spacelab-ufsc/interface-board/hardware/outputs/board_schematics/board_full_pdf_iip_charge.PDF

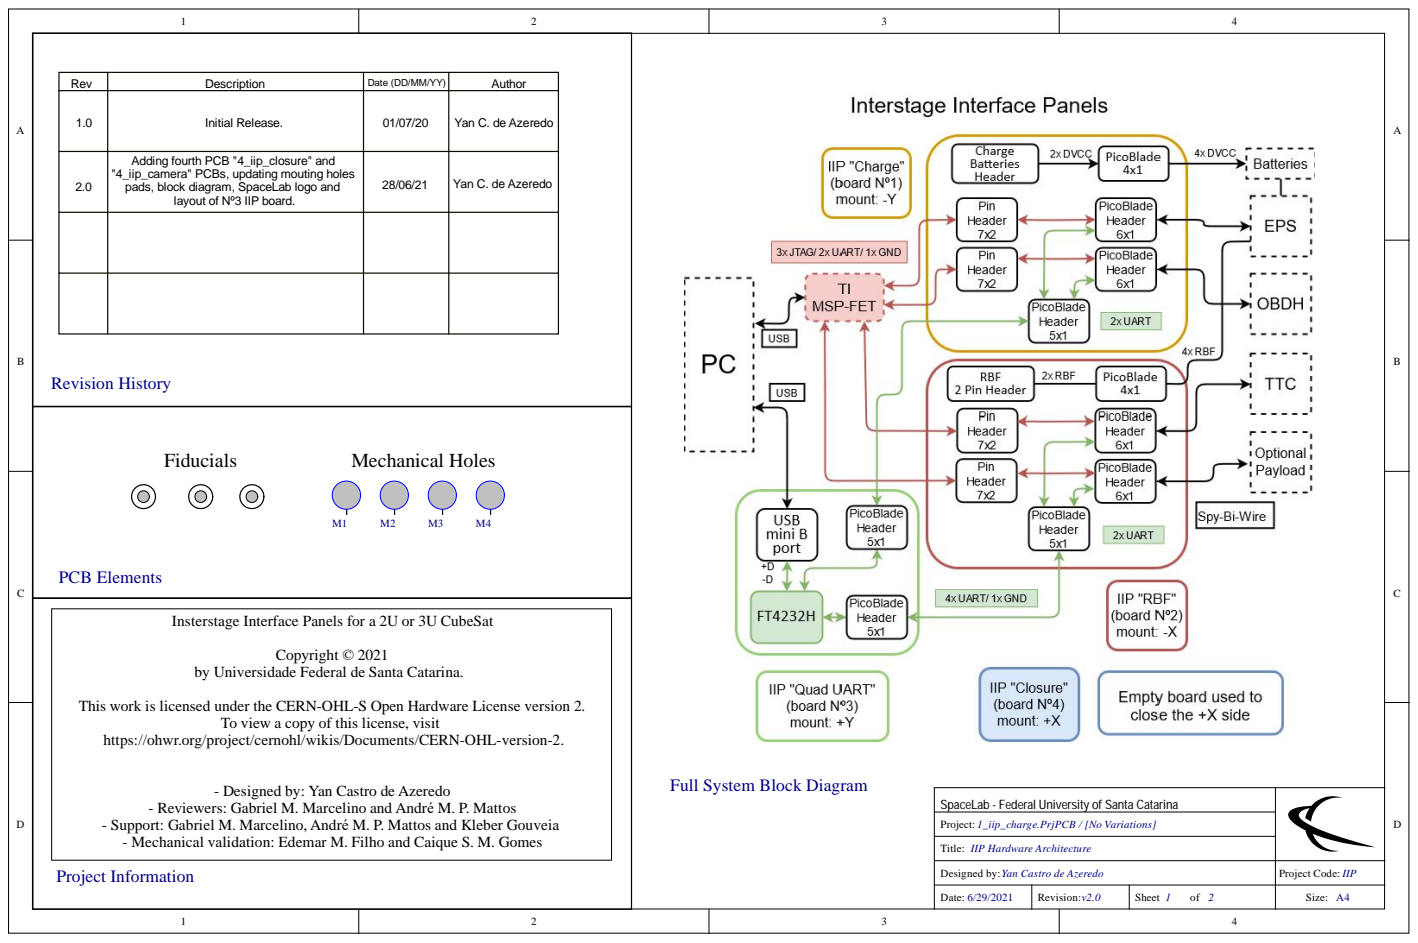
[picture p55: page 1]

R e v | D escri p t i o n | D a t e (D D /MM/YY) | Au t h o r

1 . 0 | I n i t i a l R e l e ase . | 0 1 / 0 7/2 0 | Ya n C . d e Azere d o

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

Insterstage Interface Panels for a 2U or 3U CubeSat

Universidade Federal de Santa Catarina.

the CERN-O
To view a copy of
.org/project/cernohl

Full System Block Diagram

ceLab - Federal University of S

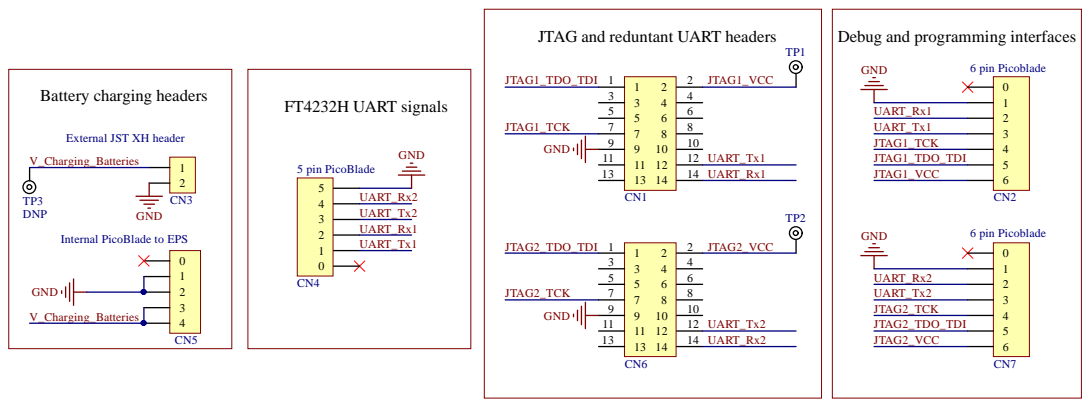
[picture p56: page 2]

tery charging headers External JST XH header

ceLab - Federal University of S

Des i g ned b y : Ya n Ca s t ro de A zered o | Project Co de: IIPN1

Date: 6 / 2 9 / 2 0 2 1 | Rev i s i o n : v2.0 | Sheet 2 o f 2 | Size: A 4

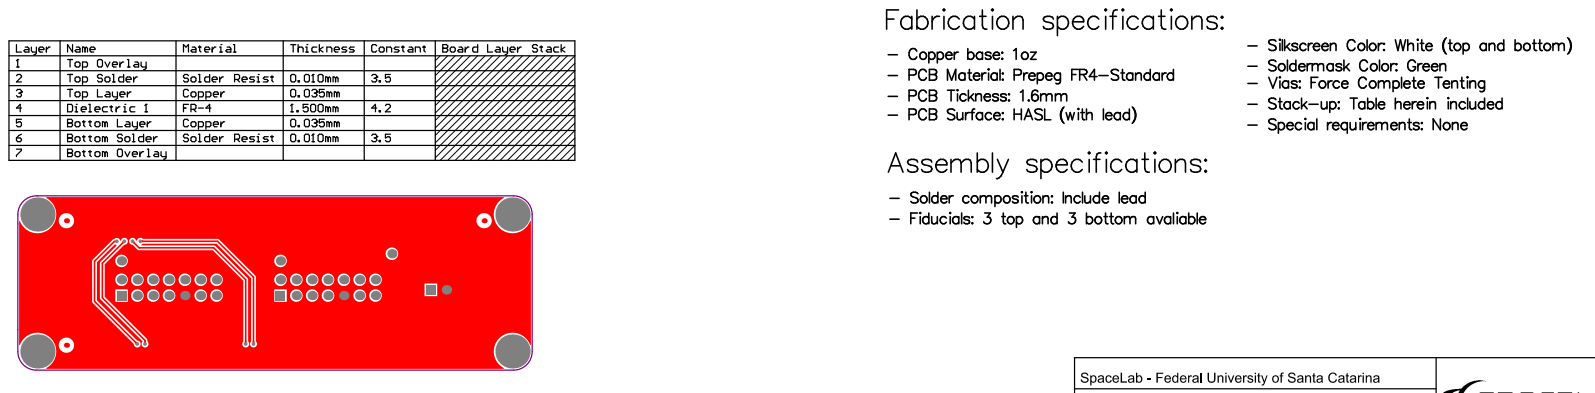
[picture p57: page 3]

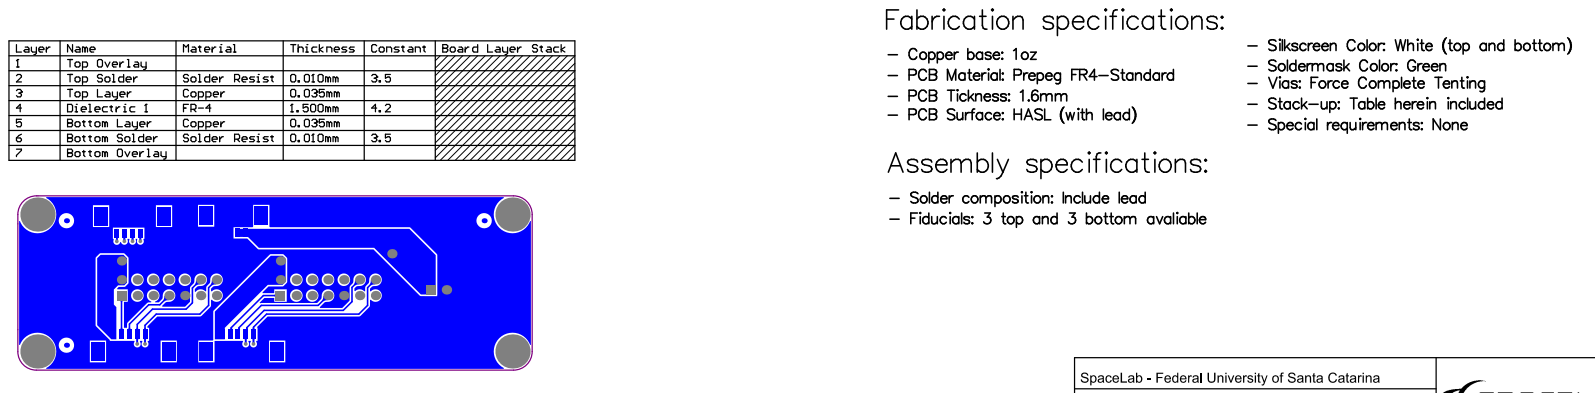
[picture p58: page 4]

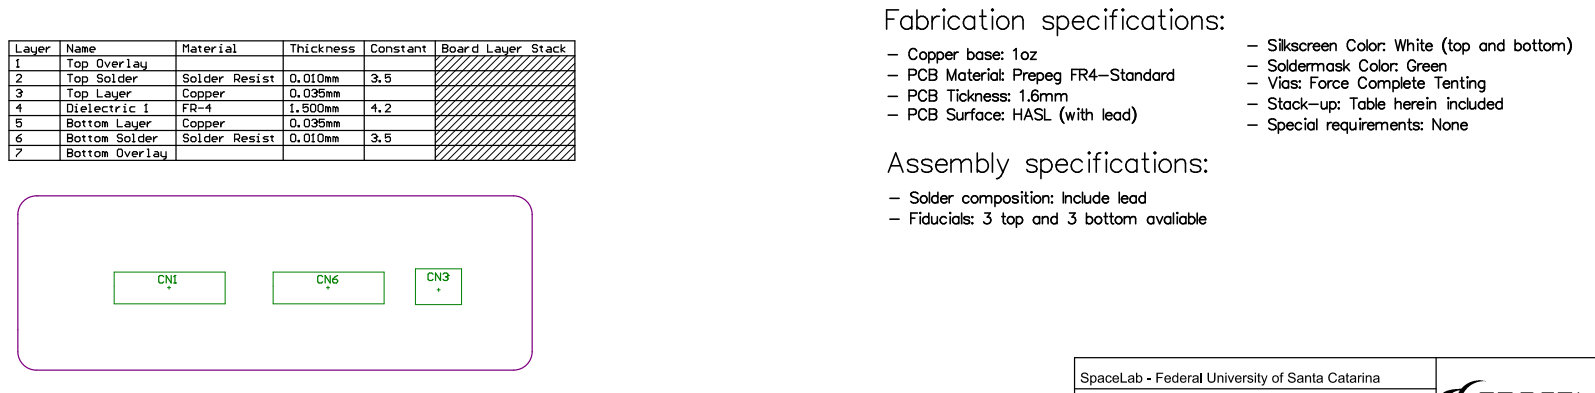
[picture p59: page 5]

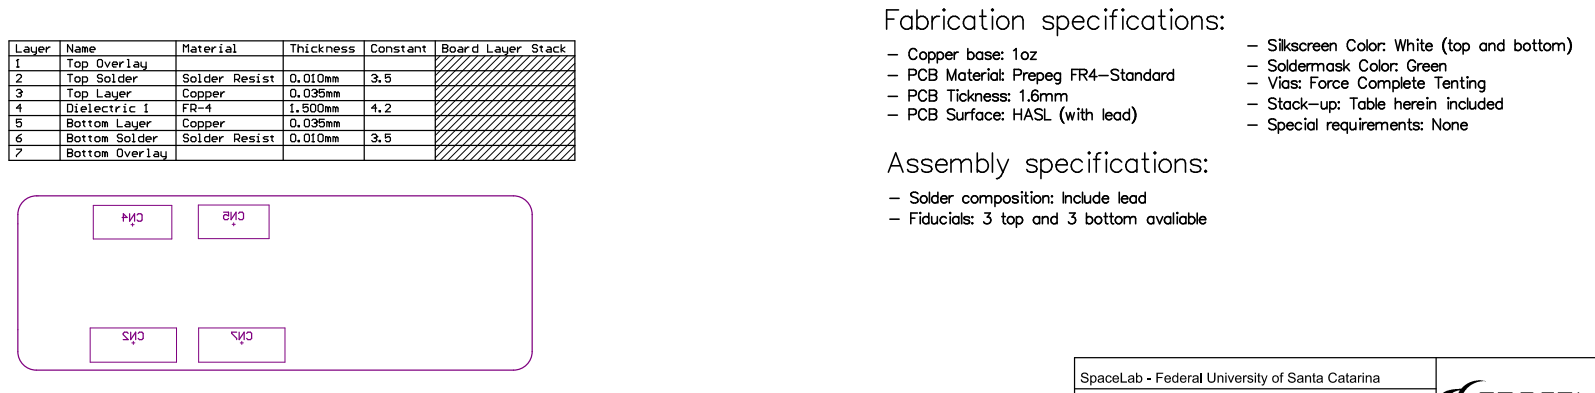
[picture p60: page 6]

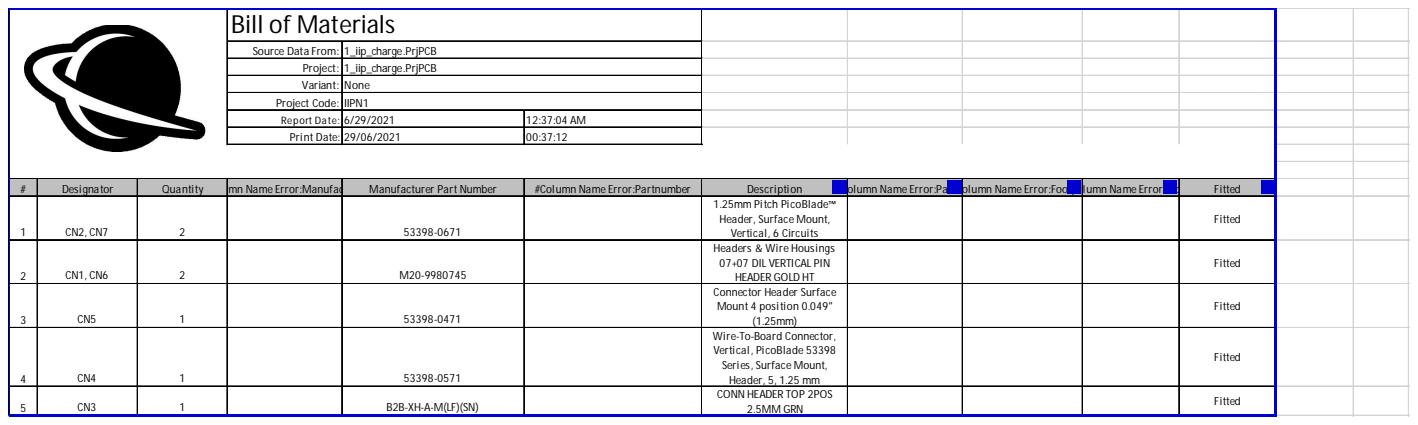
[picture p61: page 7]

Bill of Materials

Source Data From: | 1_iip_charge.PrjPCB

Project: | 1_iip_charge.PrjPCB
Variant: | None
Project Code: | IIPN1
Report Date: | 6/29/2021 | 12:37:04 AM
Print Date: | 29/06/2021 | 00:37:12

# | Designator | Quantity#Column Name Error:Manufac | Manufacturer Part Number | #Column Name Error:Partnumber | Description #Column Name Error:Pac#kaColumn Name Error:Foo#tCoprlumn Name Error:Mo | Fitted
1 | CN2, CN7 | 2 | 53398-0671 | | 1.25mm Pitch PicoBlade™ Header, Surface Mount, Vertical, 6 Circuits | Fitted

2 | CN1, CN6 | 2 | M20-9980745 | | Headers & Wire Housings 07+07 DIL VERTICAL PIN HEADER GOLD HT | Fitted

3 | CN5 | 1 | 53398-0471 | | Connector Header Surface Mount 4 position 0.049" (1.25mm) | Fitted

4 | CN4 | 1 | 53398-0571 | | Wire-To-Board Connector, Vertical, PicoBlade 53398 Series, Surface Mount, Header, 5, 1.25 mm | Fitted

5 | CN3 | 1 | B2B-XH-A-M(LF)(SN) | | CONN HEADER TOP 2POS 2.5MM GRN | Fitted
