spacelab-ufsc/interface-board/hardware/outputs/board_schematics/board_full_pdf_iip_quad_uart.PDF

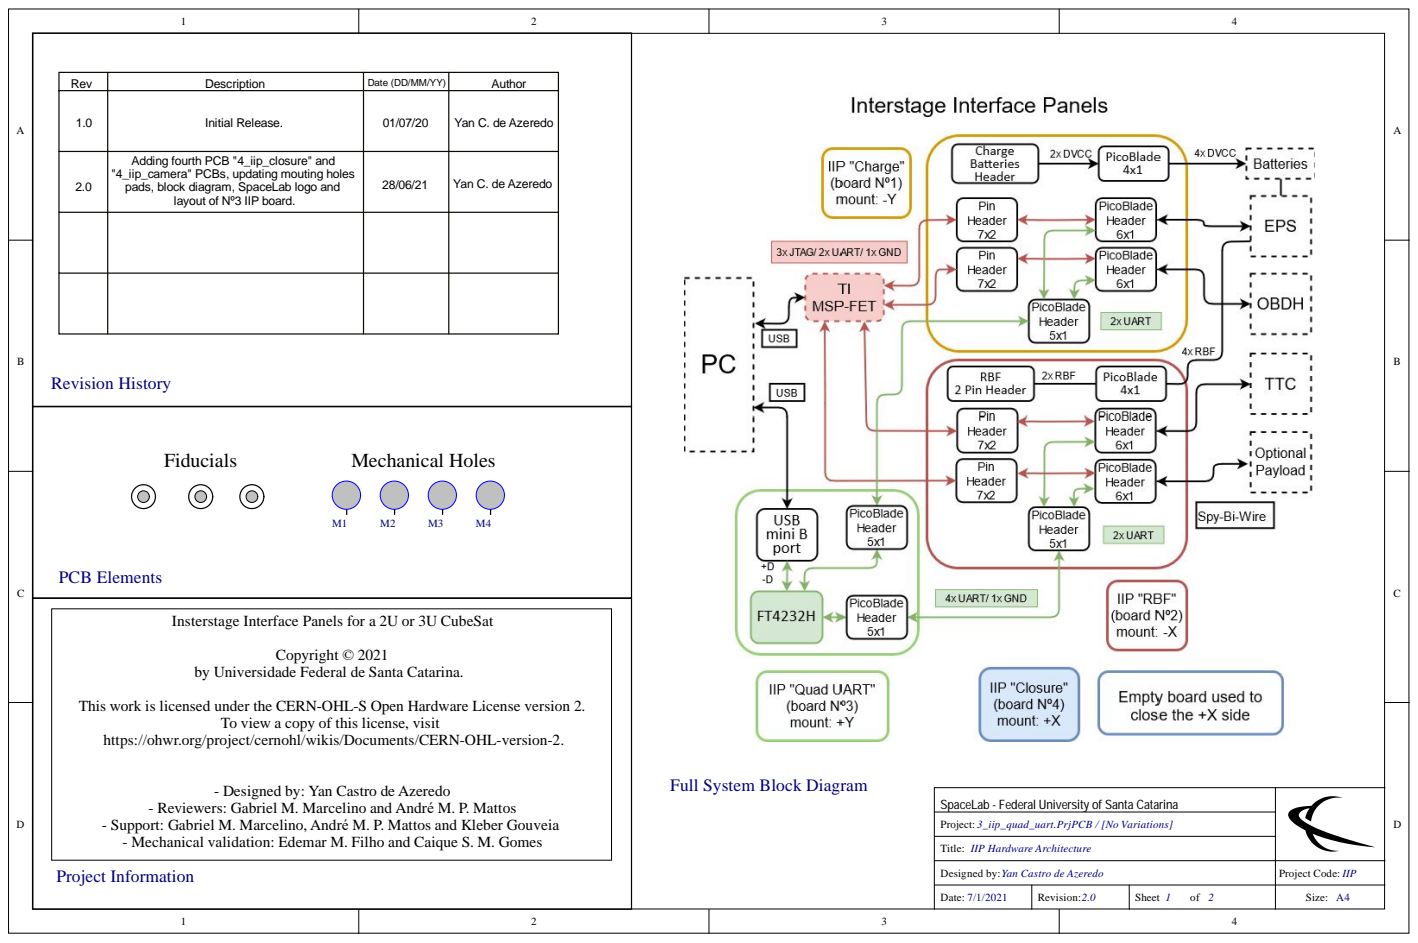
[picture p62: page 1]

R e v | D escri p t i o n | D a t e (D D /MM/YY) | Au t h o r

1 . 0 | I n i t i a l R e l e ase . | 0 1 / 0 7/2 0 | Ya n C . d e Azere d o

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

Insterstage Interface Panels for a 2U or 3U CubeSat

Universidade Federal de Santa Catarina.

the CERN-O
To view a copy of
.org/project/cernohl

Full System Block Diagram

SpaceLab - Federal University of S

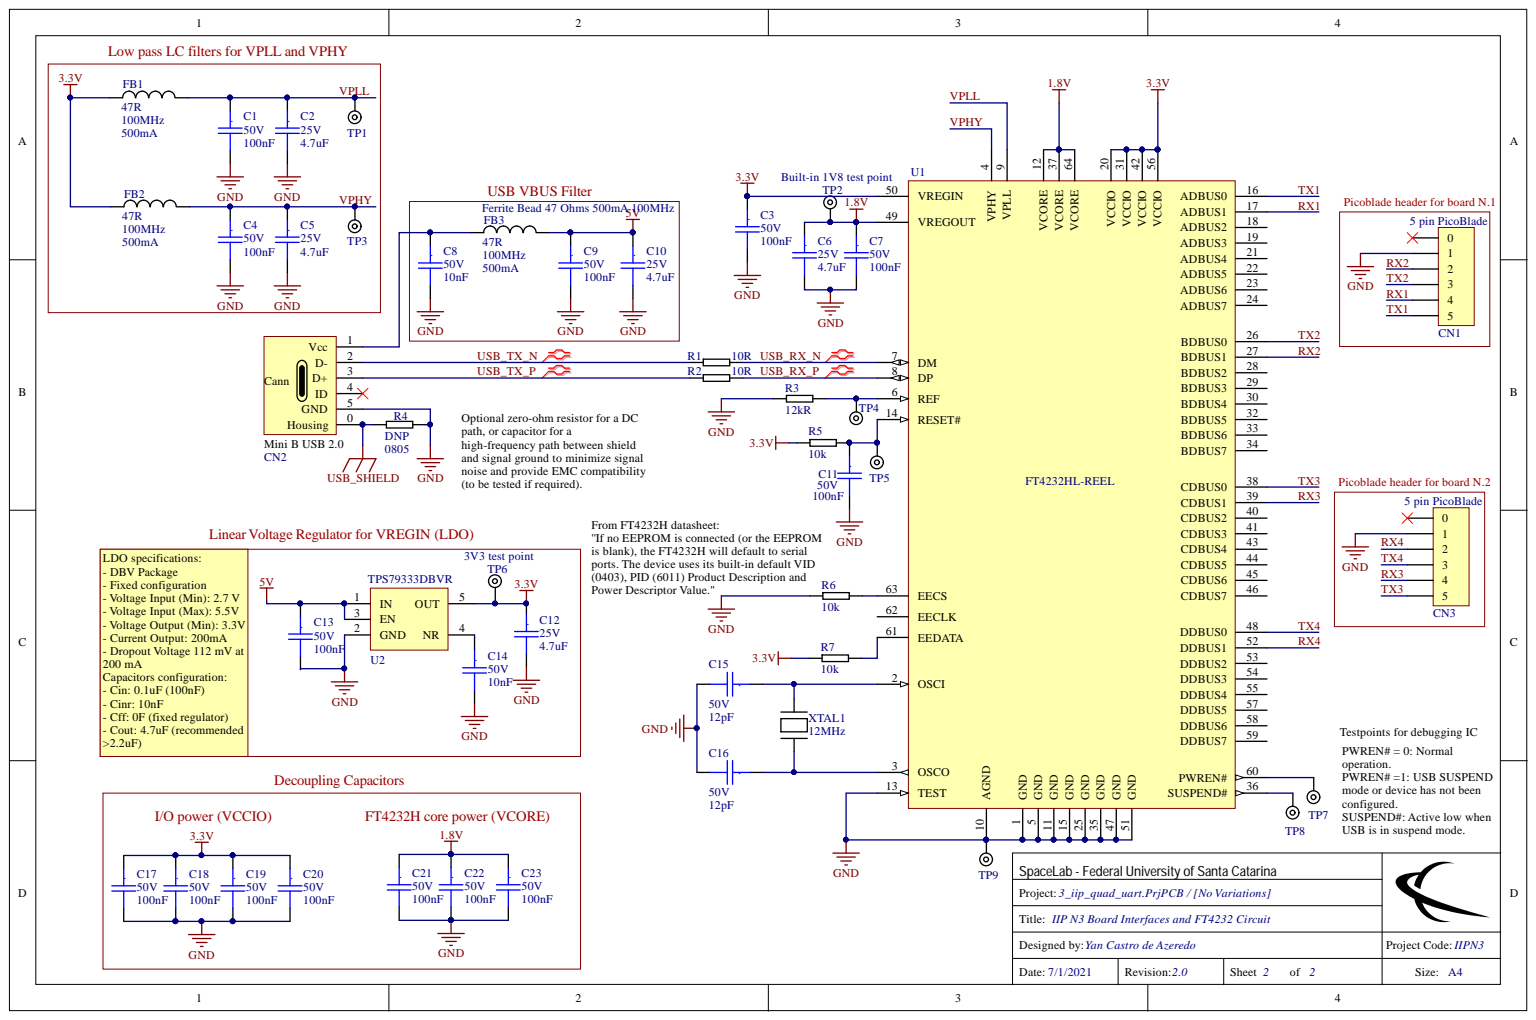
[picture p63: page 2]

ass LC filters for VPLL a

ulator for VREGIN (LDO)

SpaceLab - Federal University of S

t2 Des i g ned b y : Ya n Ca s t ro de A zered o | Project Co de: IIPN3

Date: 7 / 1 / 2 0 2 1 | Rev i s i o n : 2.0 | Sheet o f 2 | Size: A 4

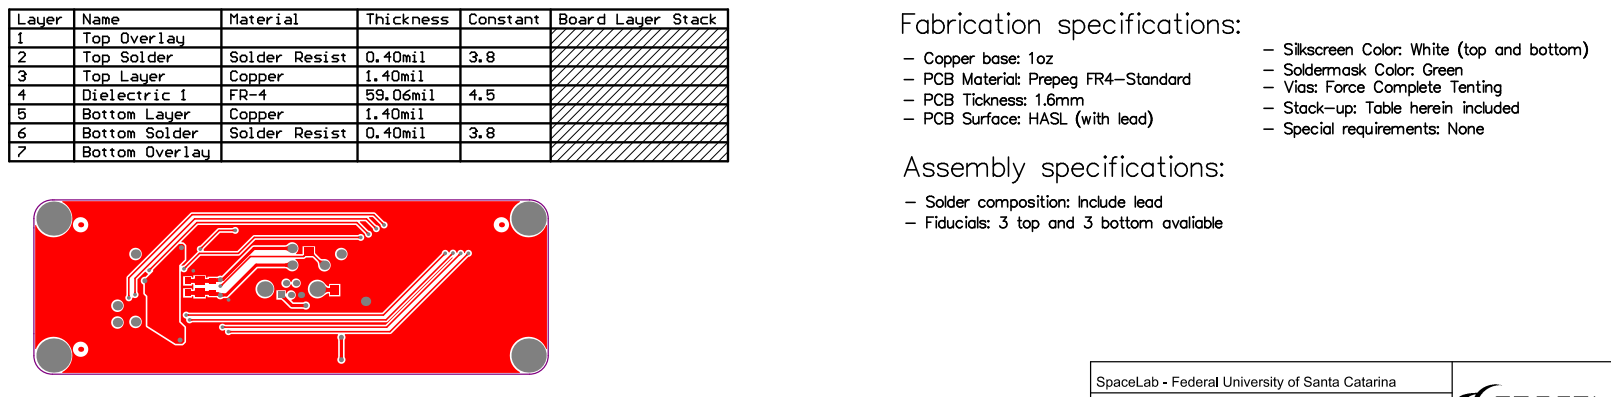
[picture p64: page 3]

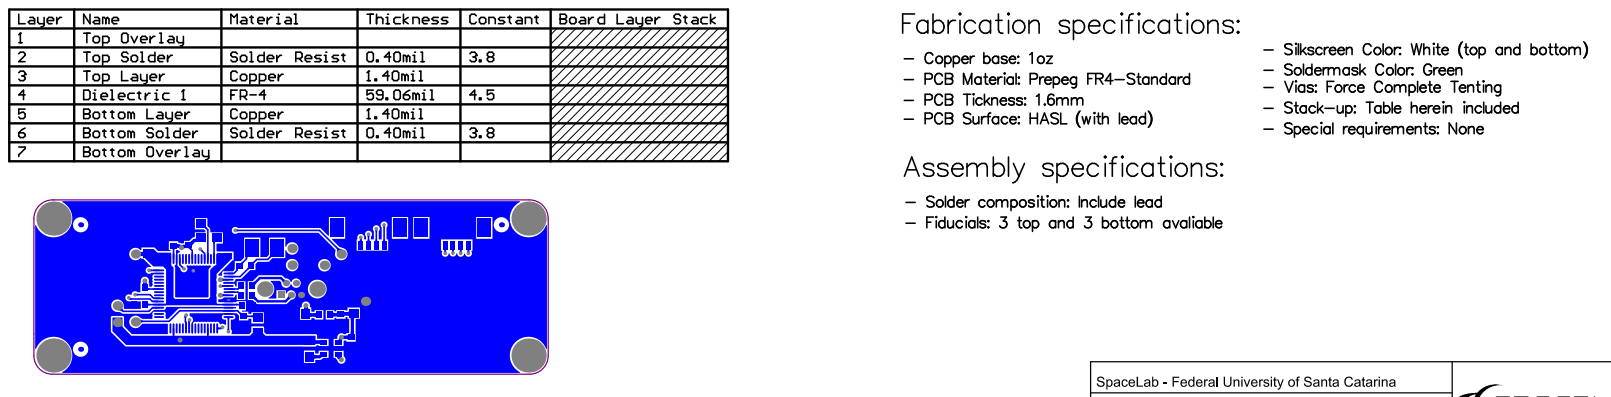
[picture p65: page 4]

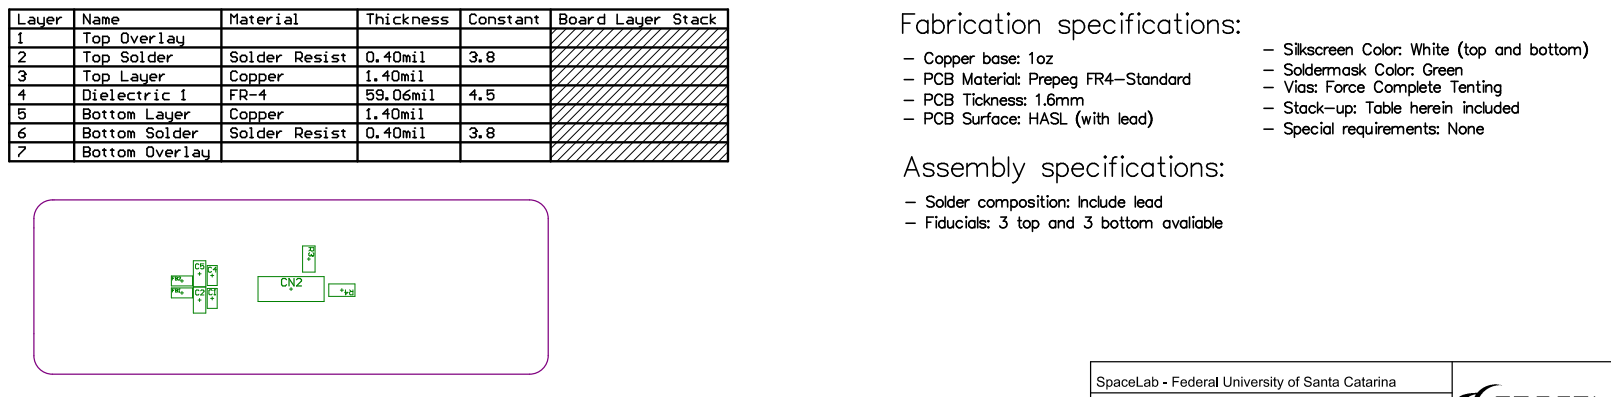
[picture p66: page 5]

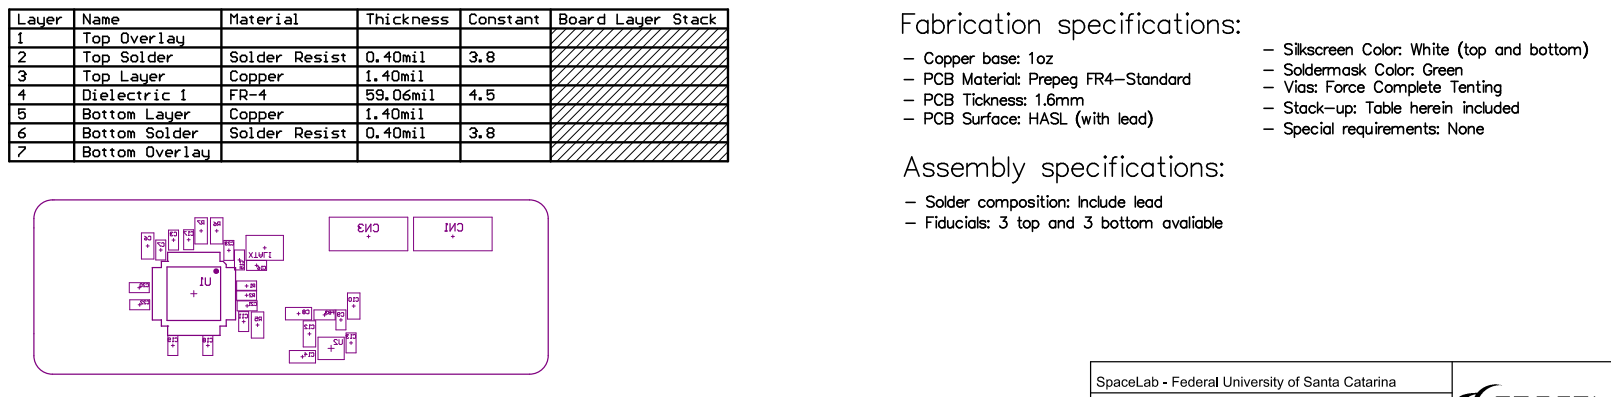
[picture p67: page 6]

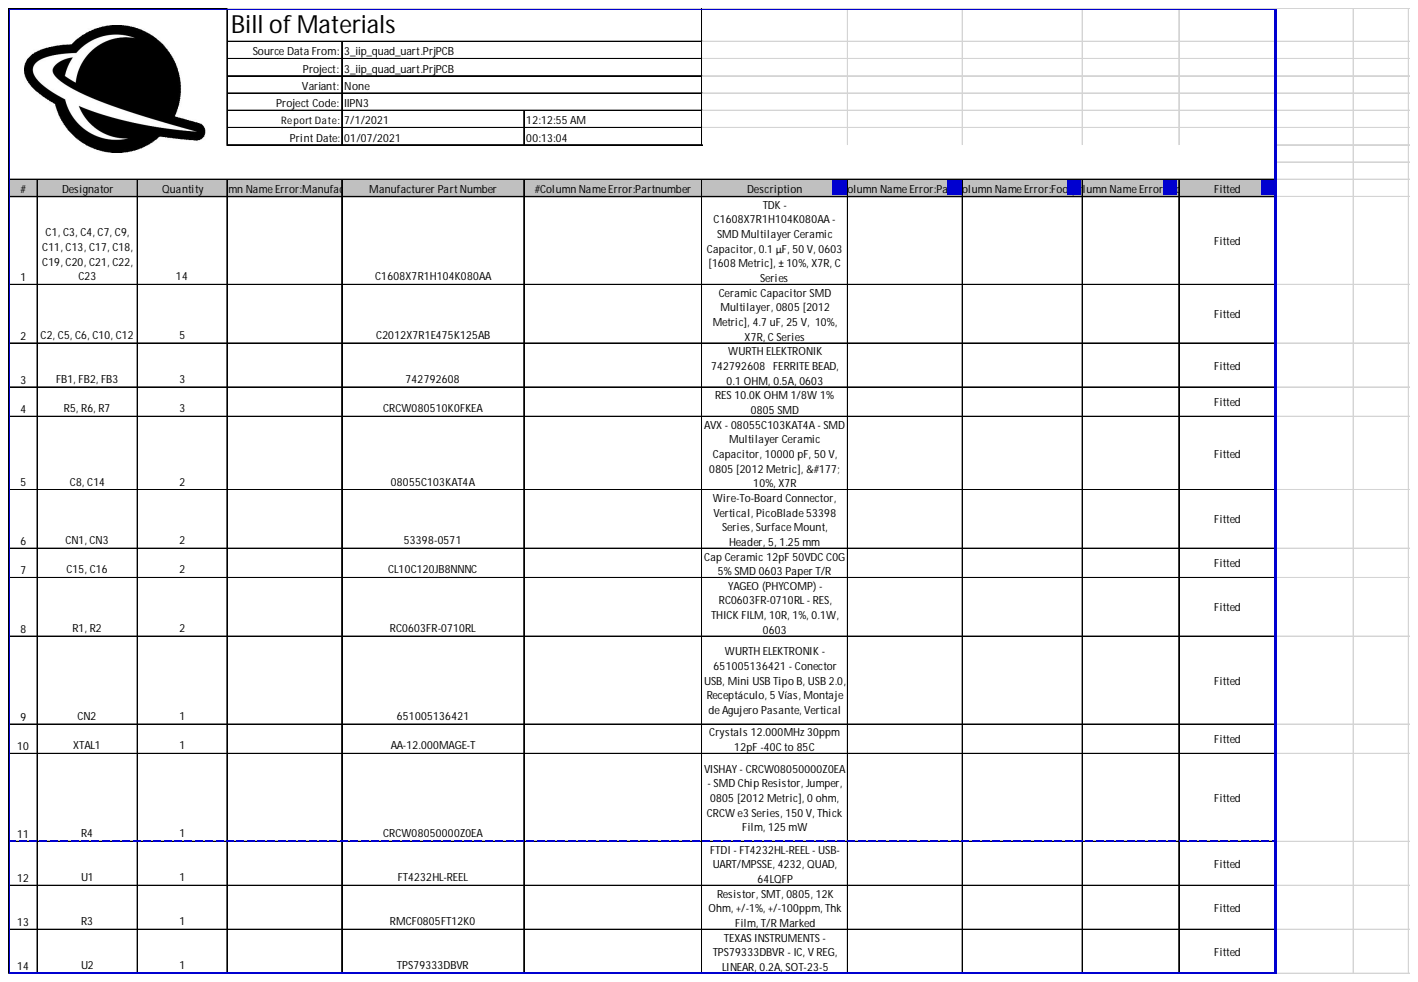
[picture p68: page 7]

Bill of Materials

Source Data From: | 3_iip_quad_uart.PrjPCB

Project: | 3_iip_quad_uart.PrjPCB
Variant: | None
Project Code: | IIPN3
Report Date: | 7/1/2021 | 12:12:55 AM
Print Date: | 01/07/2021 | 00:13:04

# | Designator | Quantity#Column Name Error:Manufac | Manufacturer Part Number | #Column Name Error:Partnumber | Description #Column Name Error:Pac#kaColumn Name Error:Foo#tCoprlumn Name Error:Mo | Fitted
1 | C1, C3, C4, C7, C9, C11, C13, C17, C18, C19, C20, C21, C22, C23 | 14 | C1608X7R1H104K080AA | | TDK -C1608X7R1H104K080AA -SMD Multilayer Ceramic Capacitor, 0.1 µF, 50 V, 0603 [1608 Metric], ± 10%, X7R, C Series | Fitted

2 | C2, C5, C6, C10, C12 | 5 | C2012X7R1E475K125AB | | Ceramic Capacitor SMD Multilayer, 0805 [2012 Metric], 4.7 uF, 25 V, 10%, X7R, C Series | Fitted

3 | FB1, FB2, FB3 | 3 | 742792608 | | WURTH ELEKTRONIK 742792608 FERRITE BEAD, 0.1 OHM, 0.5A, 0603 | Fitted

4 | R5, R6, R7 | 3 | CRCW080510K0FKEA | | RES 10.0K OHM 1/8W 1% 0805 SMD | Fitted

5 | C8, C14 | 2 | 08055C103KAT4A | | AVX - 08055C103KAT4A - SMD Multilayer Ceramic Capacitor, 10000 pF, 50 V, 0805 [2012 Metric], &#177; 10%, X7R | Fitted

6 | CN1, CN3 | 2 | 53398-0571 | | Wire-To-Board Connector, Vertical, PicoBlade 53398 Series, Surface Mount, Header, 5, 1.25 mm | Fitted

7 | C15, C16 | 2 | CL10C120JB8NNNC | | Cap Ceramic 12pF 50VDC C0G 5% SMD 0603 Paper T/R | Fitted

8 | R1, R2 | 2 | RC0603FR-0710RL | | YAGEO (PHYCOMP) -RC0603FR-0710RL - RES, THICK FILM, 10R, 1%, 0.1W, 0603 | Fitted

9 | CN2 | 1 | 651005136421 | | WURTH ELEKTRONIK -651005136421 - Conector USB, Mini USB Tipo B, USB 2.0, Receptáculo, 5 Vías, Montaje de Agujero Pasante, Vertical | Fitted

10 | XTAL1 | 1 | AA-12.000MAGE-T | | Crystals 12.000MHz 30ppm 12pF -40C to 85C | Fitted

11 | R4 | 1 | CRCW08050000Z0EA | | VISHAY - CRCW08050000Z0EA - SMD Chip Resistor, Jumper, 0805 [2012 Metric], 0 ohm, CRCW e3 Series, 150 V, Thick Film, 125 mW | Fitted

12 | U1 | 1 | FT4232HL-REEL | | FTDI - FT4232HL-REEL - USB-UART/MPSSE, 4232, QUAD, 64LQFP | Fitted

13 | R3 | 1 | RMCF0805FT12K0 | | Resistor, SMT, 0805, 12K Ohm, +/-1%, +/-100ppm, Thk Film, T/R Marked | Fitted

14 | U2 | 1 | TPS79333DBVR | | TEXAS INSTRUMENTS -TPS79333DBVR - IC, V REG, LINEAR, 0.2A, SOT-23-5 | Fitted
