spacelab-ufsc/interface-board/hardware/outputs/board_schematics/board_schematics_iip_charge.PDF

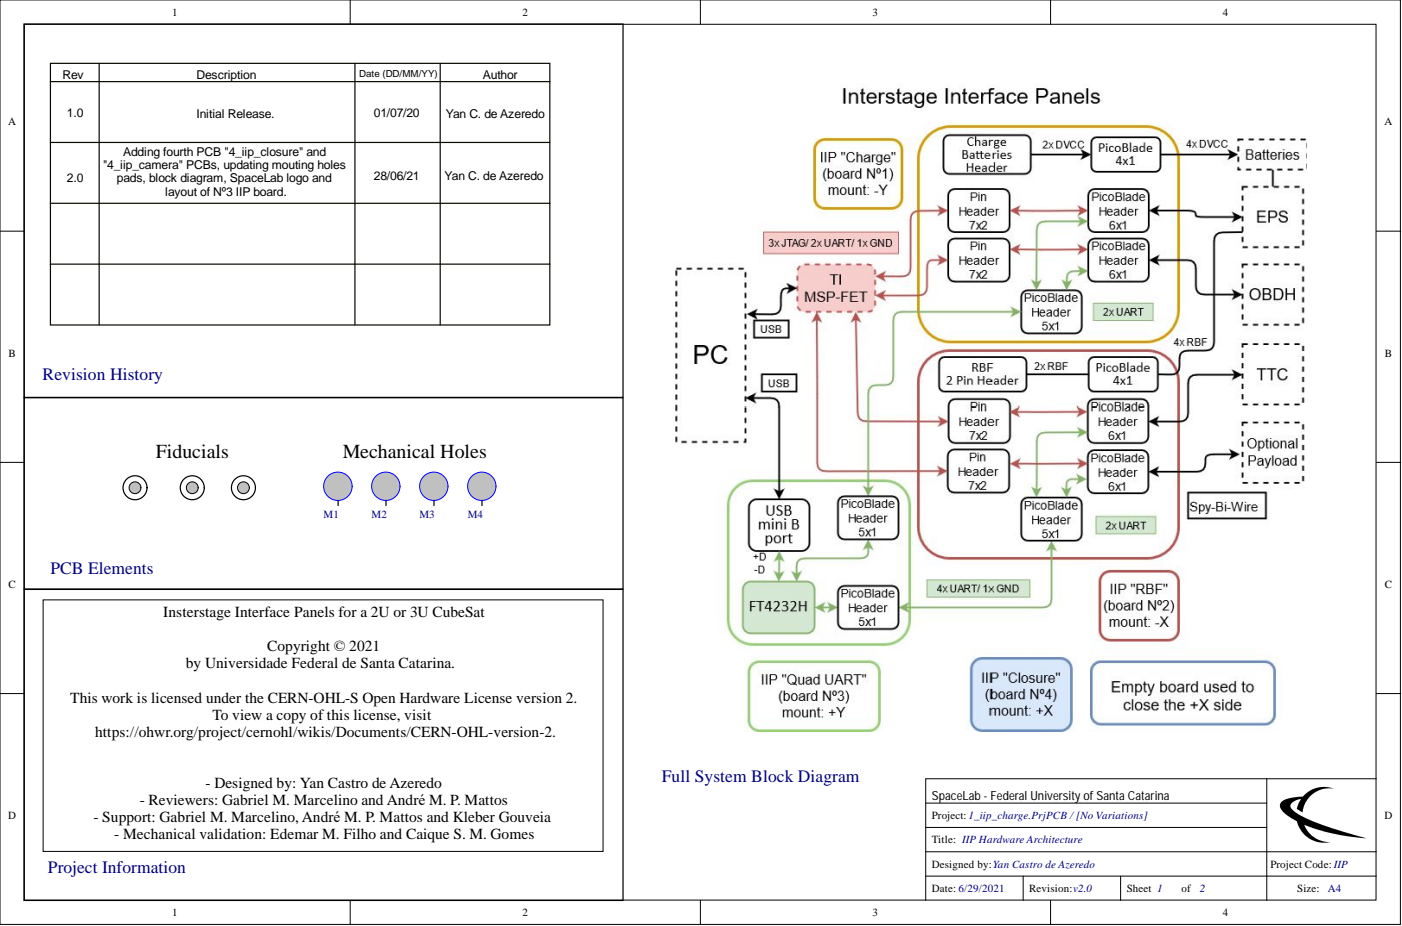
[picture p76: page 1]

R e v | D escri p t i o n | D a t e (D D /MM/YY) | Au t h o r

1 . 0 | I n i t i a l R e l e ase . | 0 1 / 0 7/2 0 | Ya n C . d e Azere d o

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

Insterstage Interface Panels for a 2U or 3U CubeSat

Universidade Federal de Santa Catarina.

the CERN-O
To view a copy of
.org/project/cernohl

Full System Block Diagram

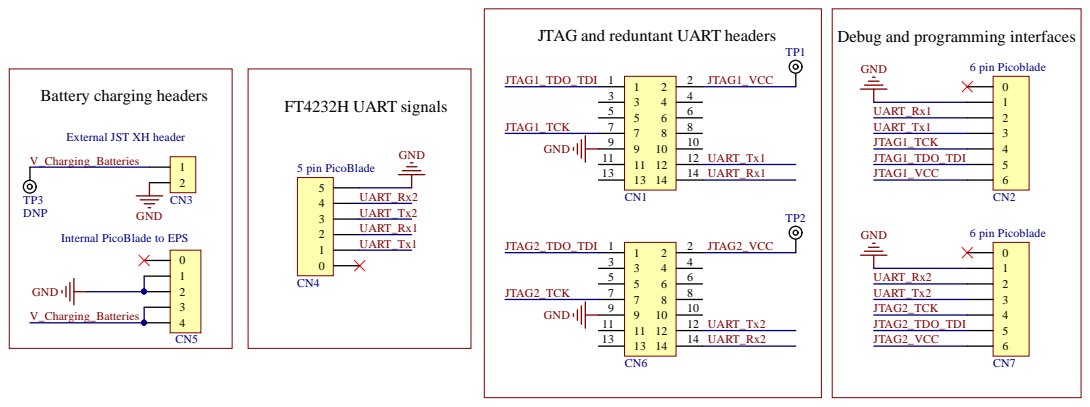
[picture p77: page 2]

tery charging headers External JST XH header

Des i g ned b y : Ya n Ca s t ro de A zered o | Project Co de: IIPN1

Date: 6 / 2 9 / 2 0 2 1 | Rev i s i o n : v2.0 | Sheet 2 o f 2 | Size: A 4
