spacelab-ufsc/interface-board/hardware/outputs/board_prints/board_prints_iip_rbf.PDF

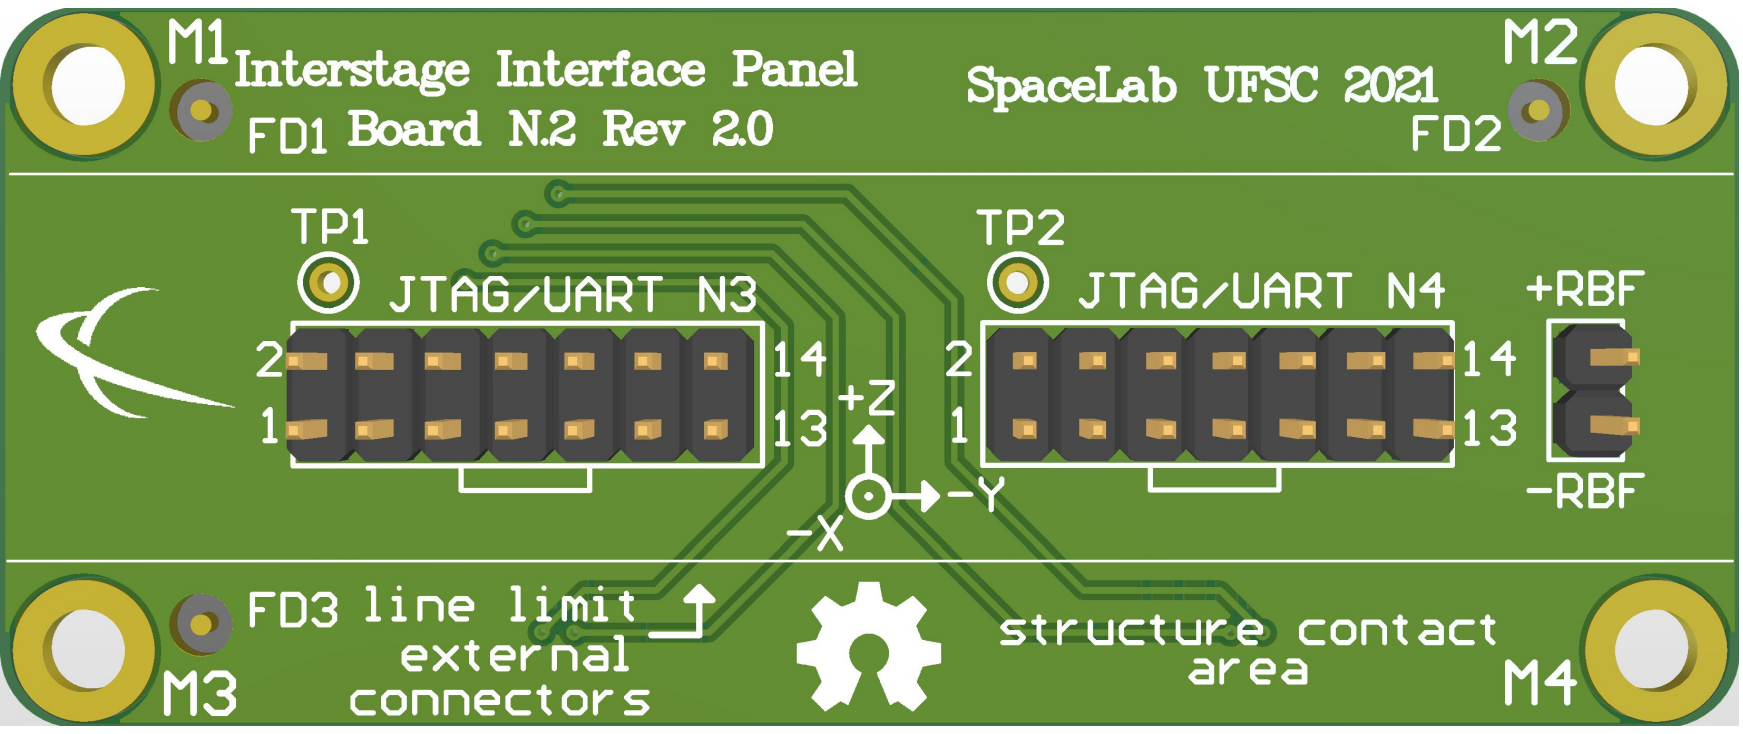
[picture p130: page 1]

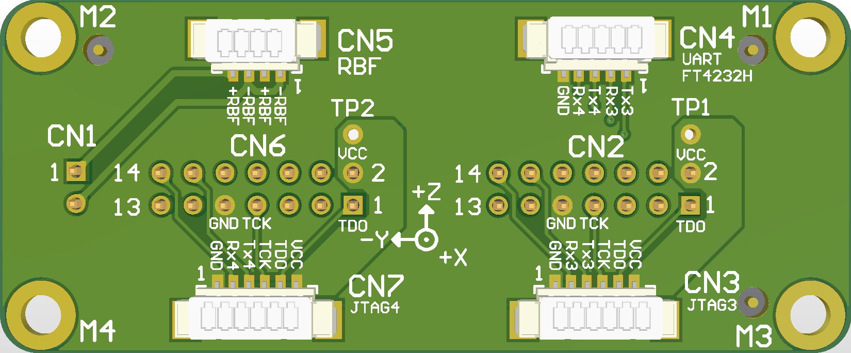
[picture p131: page 2]



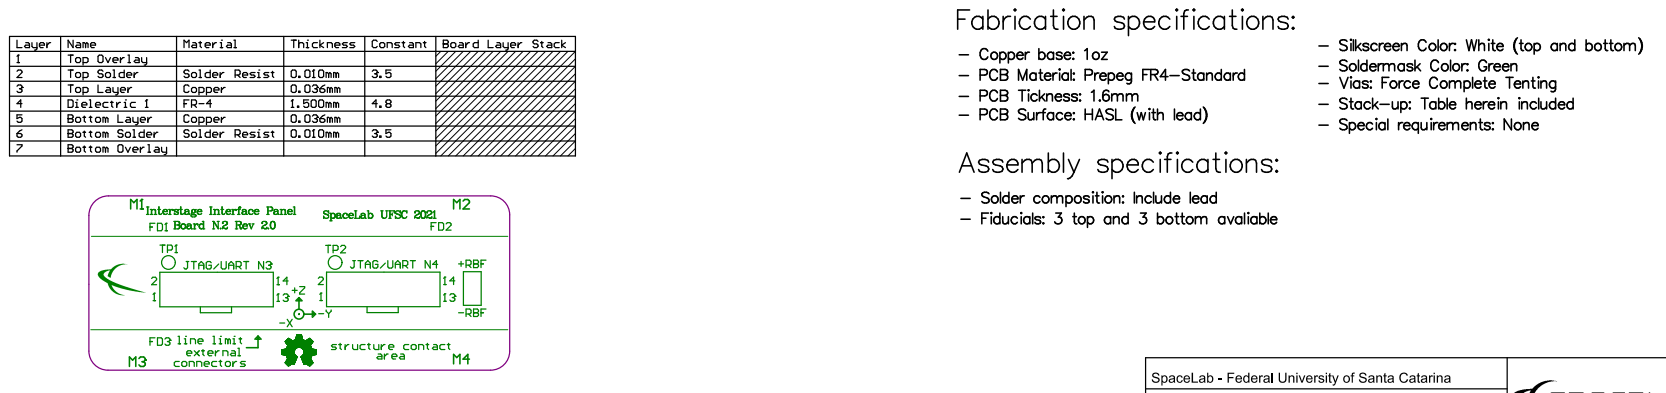
[picture p132: page 5]

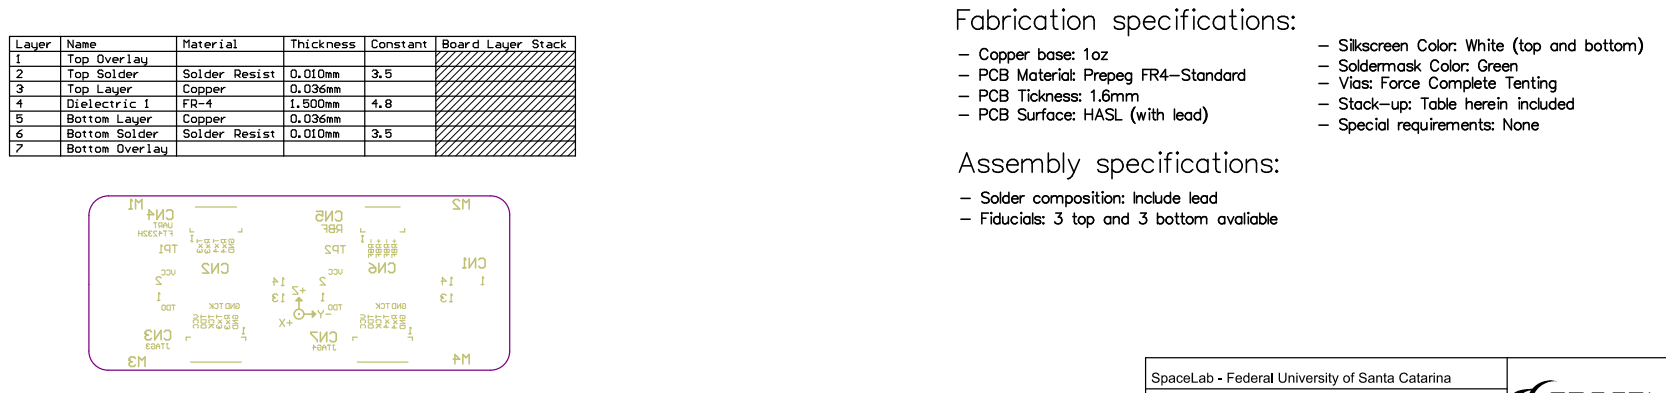
[picture p133: page 6]

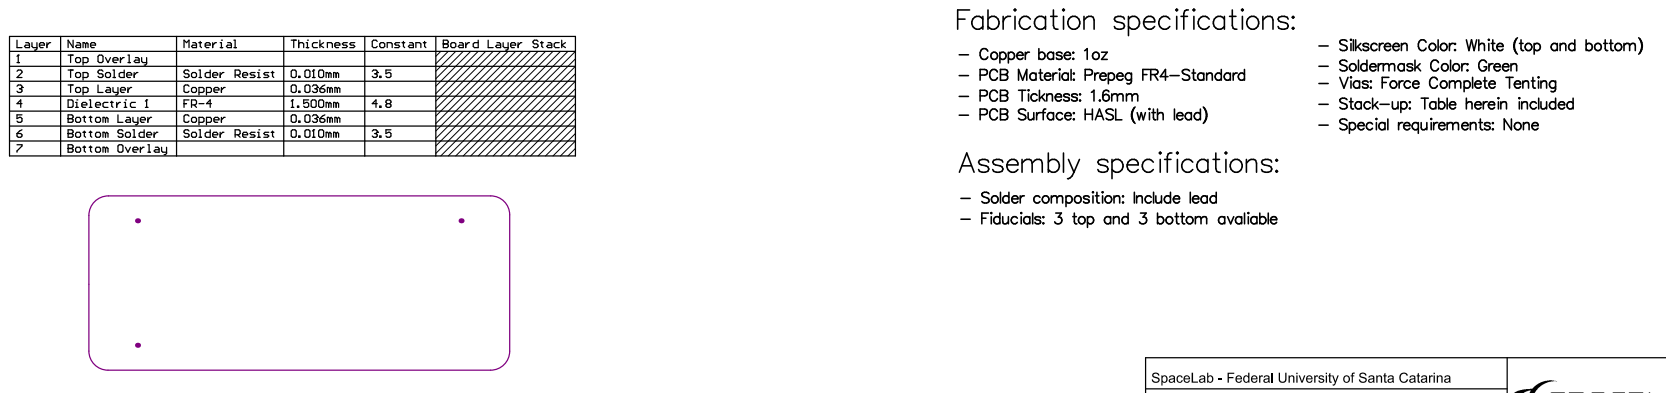
[picture p134: page 7]

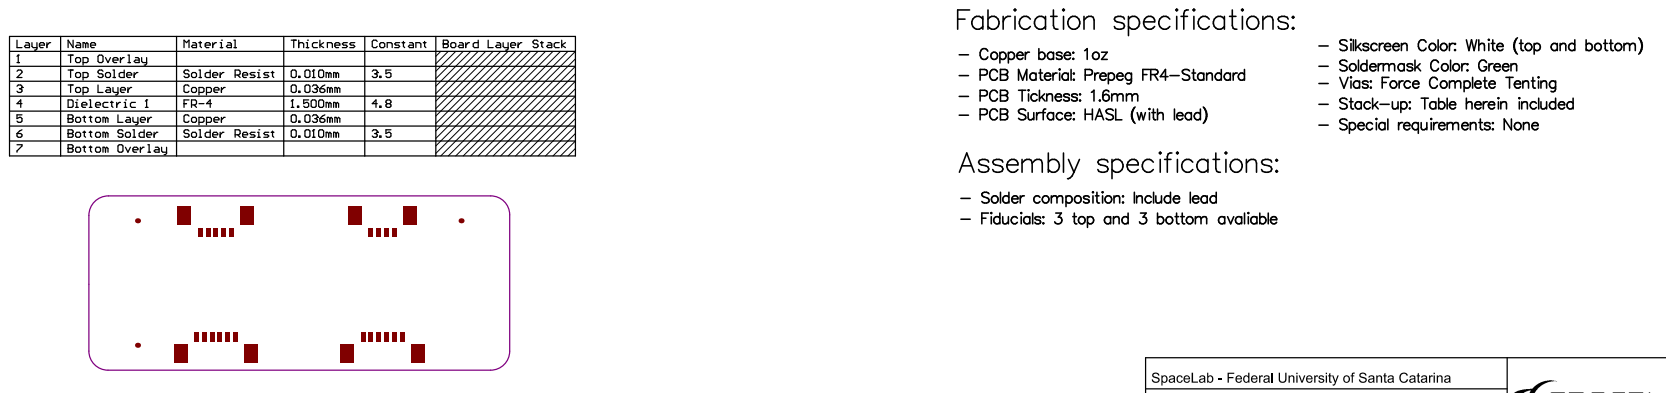
[picture p135: page 8]

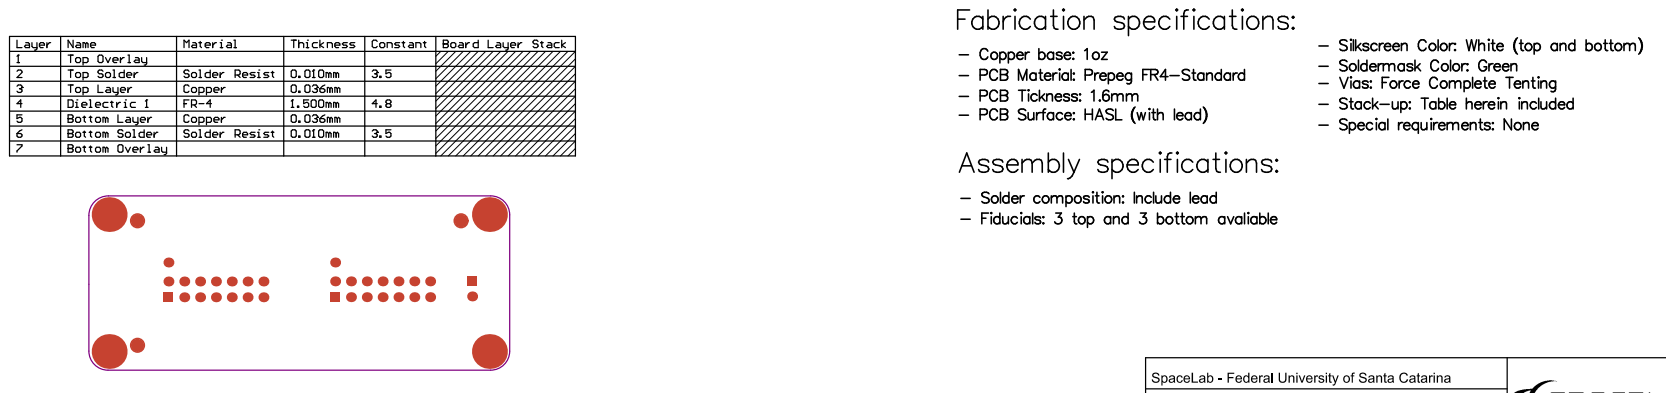
[picture p136: page 9]

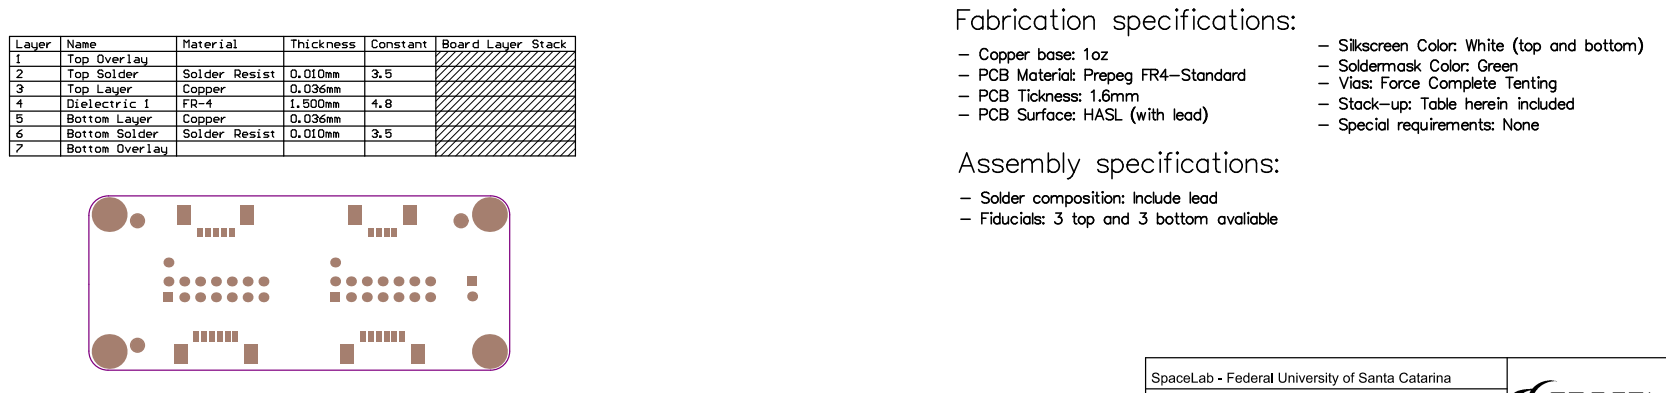
[picture p137: page 10]

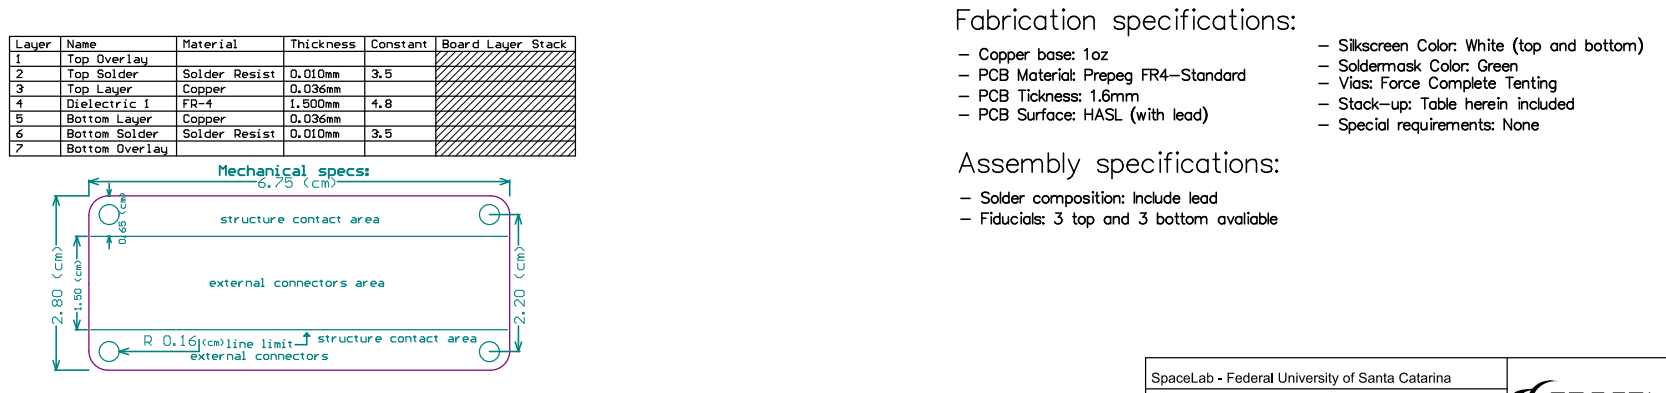
[picture p138: page 11]

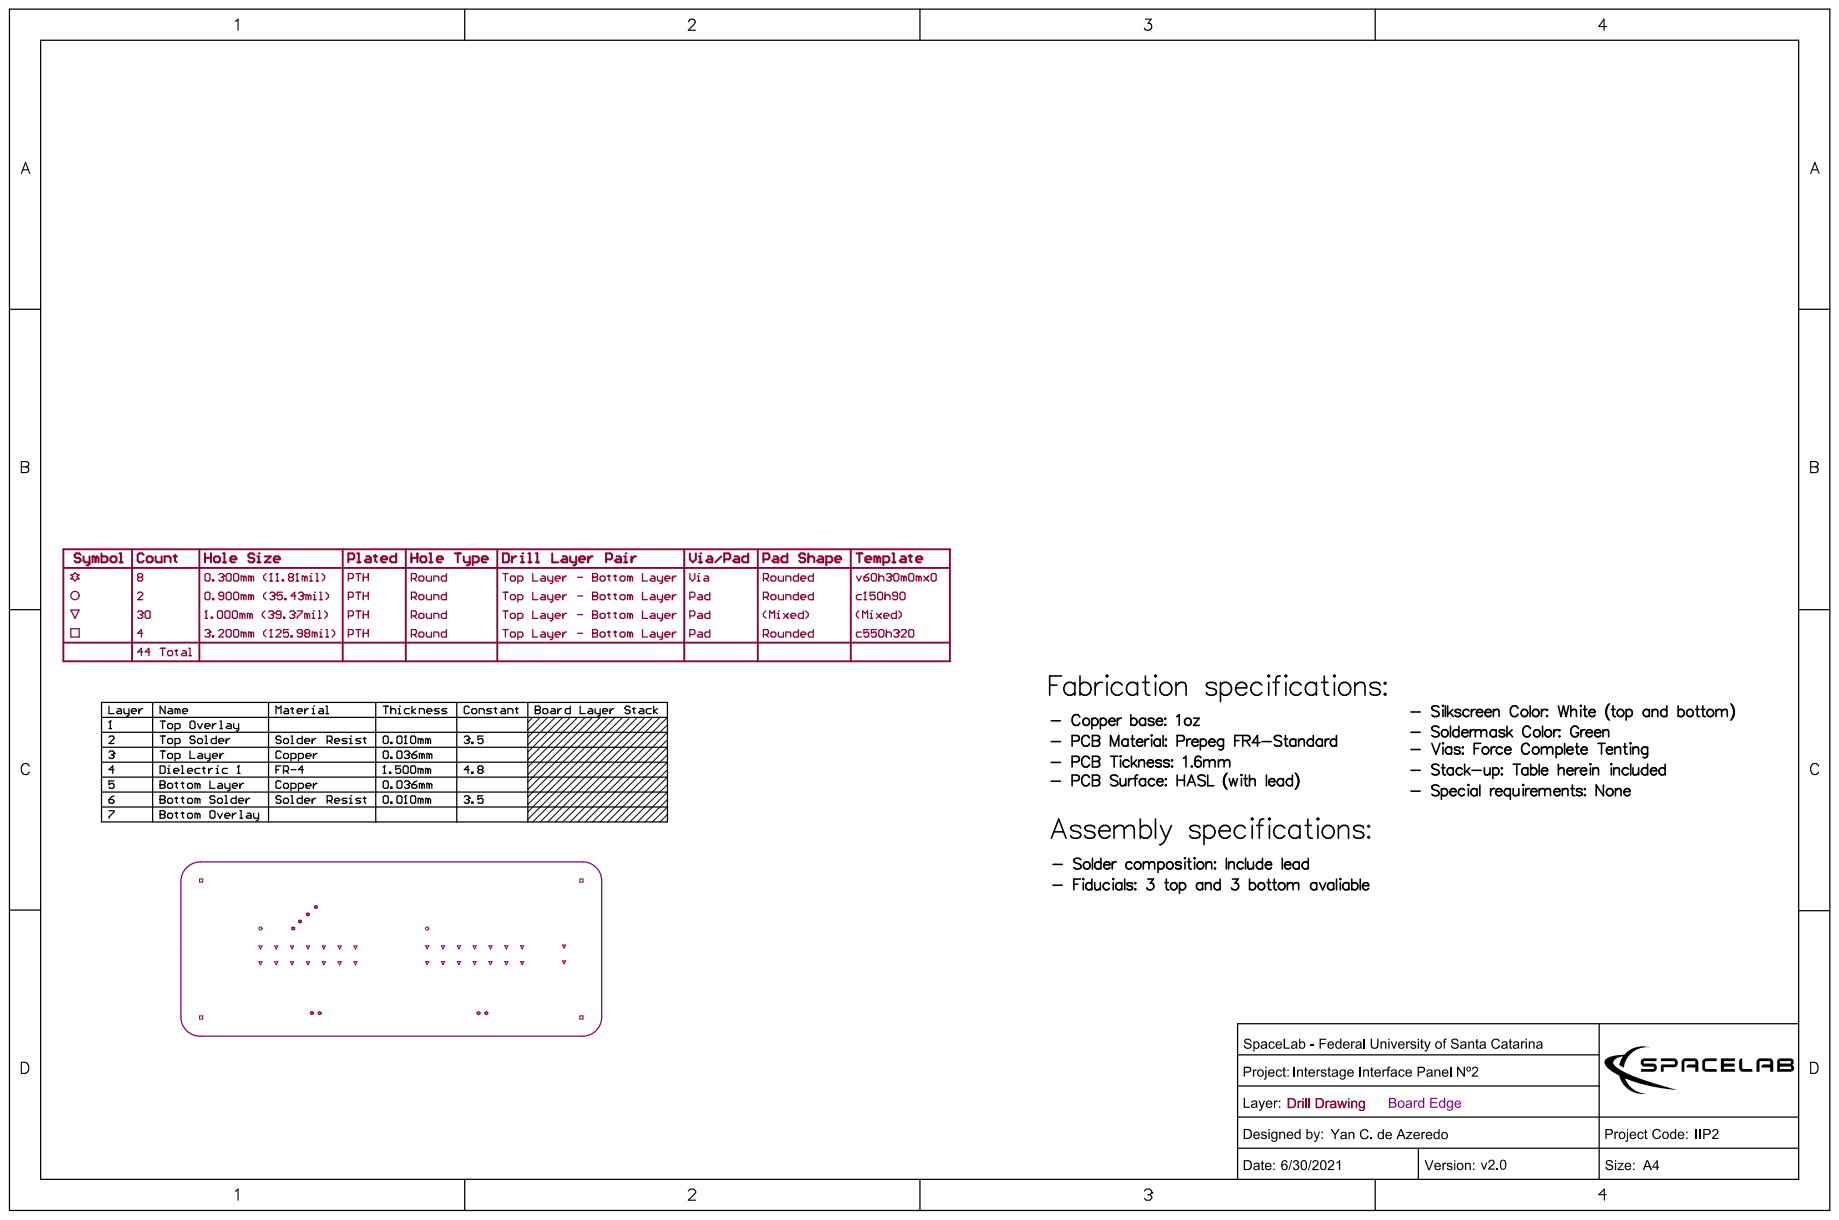
[picture p139: page 12]

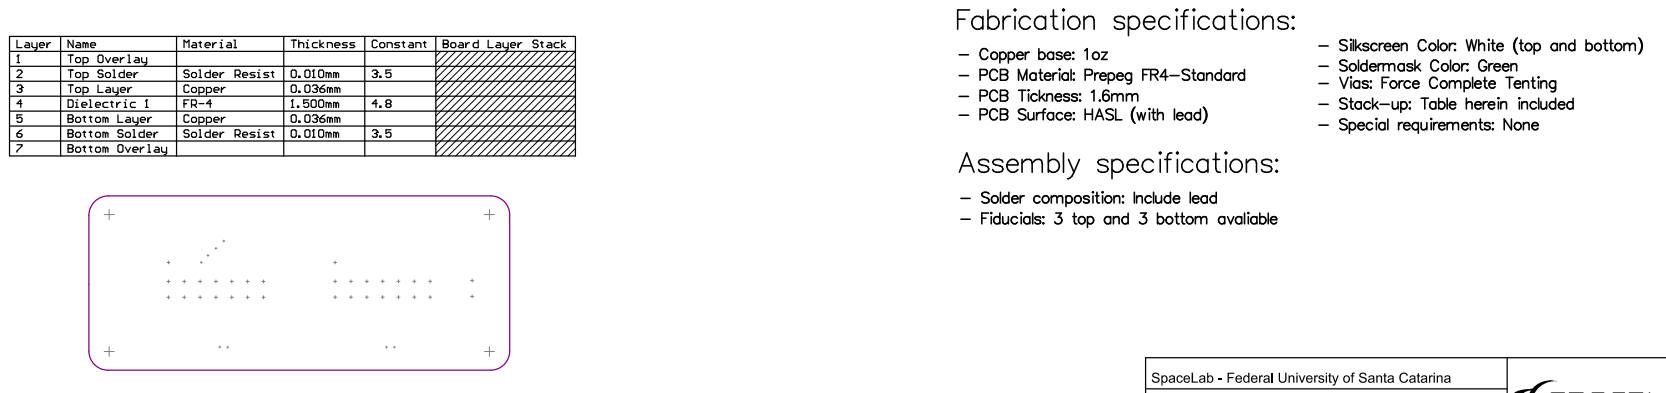
[picture p140: page 13]
